AlexanderSaal/Analog_Computer_Math_Extension_Module/Frontplate/schematic/PCB-1.png

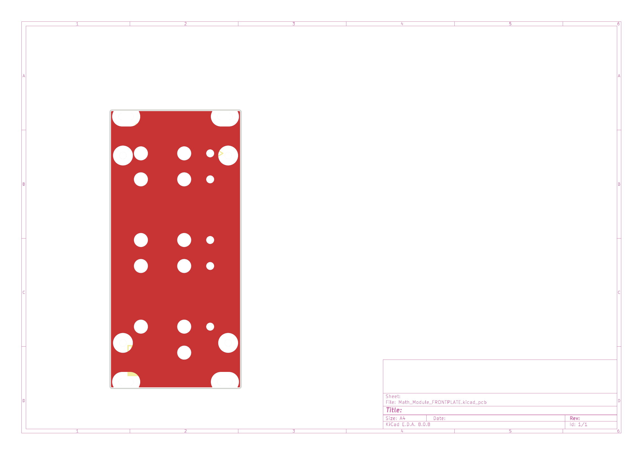
Frontplate/schematic/PCB-1.png
